NicolasCoubronne/Oulu_Embedded_Systems_Project/debug_code/motoring/Core/Inc/esp_arm.h

/*
 * esp_arm.h
 *
 *  Created on: Apr 26, 2023
 *      Author: tim
 *
 *      High-level functions for arm control (header)
 *      More documentation in implementation file
 */

#ifndef INC_ESP_ARM_H_
#define INC_ESP_ARM_H_

#include "stm32f4xx_hal.h"

int arm_angles_from_dist(unsigned int distance,
		unsigned int *angle_base_joint, unsigned int *angle_middle_joint, unsigned int *angle_claw_joint);
unsigned int offset_base_angle(unsigned int distance, double claw_offset);

#endif /* INC_ESP_ARM_H_ */
