NicolasCoubronne/Oulu_Embedded_Systems_Project/debug_code/motoring/Core/Src/esp_fsm.c

/*
 * esp_fsm.c
 *
 *  Created on: Apr 25, 2023
 *      Author: Jussi Virtanen
 *
 *  Robot arm state machine
 */

#include <stdio.h>
#include <math.h>
#include <stdlib.h>

#include "main.h"
#include "stm32f4xx_hal.h"
#include "tof.h"

#include "esp_ax12a.h"
#include "esp_arm.h"
#include "esp_fsm.h"
#include "esp_onboard.h"

extern UART_HandleTypeDef huart1;

//Bluetooth variables
extern uint8_t buf_RX[Size];
extern uint8_t buf_TX[Size];
uint8_t buf_len;

//TOF Variables
uint32_t refSpadCount;
uint8_t isApertureSpads;
uint8_t VhvSettings;
uint8_t PhaseCal;
VL53L0X_RangingMeasurementData_t RangingData;
static VL53L0X_Error myStatus = VL53L0X_ERROR_NONE;
unsigned int sensor_distance_mm;

/*
 * Send string to bluetooth
 *
 * msg: pointer to the message
 */
void bt_send(char *msg)
{
	HAL_UART_Transmit(&huart1, (uint8_t*)msg, strlen(msg), HAL_MAX_DELAY);
}

/*
 * Get distance value from TOF sensor
 *
 * returns: approximate distance in mm
 */
unsigned int get_dist() {
	unsigned int sensor_distance_mm= 0;

	for (int i=0; i<5; i++){
		myStatus = VL53L0X_PerformSingleRangingMeasurement(TOF1, &RangingData);
		if (myStatus!=VL53L0X_ERROR_NONE) {
			Error_Handler();
		}
		//if (RangingData.RangeMilliMeter < sensor_distance_mm) sensor_distance_mm = RangingData.RangeMilliMeter;
		sensor_distance_mm += RangingData.RangeMilliMeter;
		HAL_Delay(25);
	}

	sensor_distance_mm = sensor_distance_mm/5;

	/*
	myStatus = VL53L0X_PerformSingleRangingMeasurement(TOF1, &RangingData);
	if (myStatus!=VL53L0X_ERROR_NONE) {
		Error_Handler();
	}
	*/

	//while(RangingData.RangeStatus != 0) {}

	//sensor_distance_mm = RangingData.RangeMilliMeter;
	buf_len = sprintf((char*)buf_RX, "TOF value : %d\r\n", sensor_distance_mm);
	//bt_send((char*)buf_RX);


	if(sensor_distance_mm < 100) return 1000;

	return sensor_distance_mm;
}

/* Start the arm state machine
 * Further implementation details are in the documents
 */
void arm_start_sm()
{

	//Motors variables
	unsigned int angle_ccw_edge, angle_cw_edge; // Angles where object edge were found
	unsigned int middle_rot;
	unsigned int distance_threshold_mm; // max distance where arm will consider an object to exist
	unsigned int object_offset_distance_mm;
	unsigned int ccw_seek_angle_limit, cw_seek_angle_limit; // Seek area limits
	unsigned int claw_angle_limit_open, claw_angle_limit_closed;
	unsigned int dump_angle;
	unsigned int blocked_move_timeout_ms;
	unsigned int dist;
	unsigned int angle_middle_joint_max;
	double claw_offset_mm; // mm
	int status;
	armState arm_state;

	char temp[100];

	unsigned int angle_base_joint;
	unsigned int angle_middle_joint;
	unsigned int angle_claw_joint;

	// Heuristic offsets for distance and base rotation due to claw dimensions
	object_offset_distance_mm = -85;
	claw_offset_mm = 25.0;

	// From how far do we want to find the object
	distance_threshold_mm = 350;

	// Init limits and start values
	angle_middle_joint_max = 1000; // MAx angle for middle joint, if we go higher than this, then assume object too close
	ccw_seek_angle_limit = 205; // ~90 degrees ccw
	cw_seek_angle_limit = 819; // ~90 degrees cw
	claw_angle_limit_closed = 600; // fully closed
	claw_angle_limit_open = 320; // fully open
	dump_angle = 150; // Near max limit ccw
	angle_ccw_edge = angle_cw_edge = 0; // Use 0 as the magic number where angle has not yet been found
	blocked_move_timeout_ms = 2000;

	//TOF Init
	myStatus=TOF1_VL53L0X_Init_Single(&refSpadCount,&isApertureSpads,&VhvSettings,&PhaseCal,0);
	if (myStatus!=VL53L0X_ERROR_NONE) {
		printf("TOF1 Initialization Error : %i\r\n", myStatus);
	}
	TOFX_VL53L0X_LongRangeSettings(TOF1);
	VL53L0X_StartMeasurement (TOF1);

	// Test tof

	/*
	while (1) {
		sprintf(temp, "distance: %u\n", get_dist());
		bt_send(temp);
		HAL_Delay(100);
	}*/

	//MOTOR INIT
	uint8_t ids[] = {3, 2, 9, 8, 4};
	uint16_t init_angles[] = {390, 950, 600, claw_angle_limit_open, 819};
	uint16_t init_speed[] = {30, 60, 60, 40, 20};

	for (int i=0; i < sizeof(ids)/sizeof(ids[0]); i++) {
		ax_set_move_speed(ids[i], init_speed[i]);
		HAL_Delay(500);
	}
	ax_set_max_torque(8, 200);


	arm_state = ARM_MOVE_TO_IDLE;
	while(1) {
		switch(arm_state) {

		case ARM_MOVE_TO_IDLE:
			bt_send("Entering state : ARM_MOVE_TO_IDLE\r\n");
			sprintf(temp, "Voltage data from sensor: %f\r\n", get_current_measure());
			bt_send(temp);
			// Reset object edges
			angle_ccw_edge = angle_cw_edge = 0;
			//Move to good idle position (blocked move)
			for (int i=0; i < sizeof(ids)/sizeof(ids[0]); i++) {
				ax_move_blocked(ids[i], init_angles[i], blocked_move_timeout_ms);
			}
			arm_state = ARM_SEEK_CCW;

			break;

		case ARM_SEEK_CCW:
			bt_send("Entering state : ARM_SEEK_CCW\r\n");
			set_operation_led(LED_BLINK);
			angle_ccw_edge = angle_cw_edge = 0;
			// Set goal to ccw edge if not yet set
			ax_stop(4);
			HAL_Delay(500);
			ax_set_goal_raw(4, ccw_seek_angle_limit);
			while(1){
				// If at edge, invert seek direction
				if (ax_diff_from_goal(4) <= 10) {
					HAL_Delay(1000);
					arm_state = ARM_SEEK_CW;
					break;
				}
				// cw edge found
				if ((dist = get_dist()) < distance_threshold_mm) {
					angle_cw_edge = ax_get_current_position(4);
					sprintf(temp, "Object edge CW angle: %u\r\n", angle_cw_edge);
					bt_send(temp);
					arm_state = ARM_SEEK_EDGE_CCW;
					break;
				}
				HAL_Delay(50);
			}

			break;

		case ARM_SEEK_EDGE_CCW:
			bt_send("Entering state : ARM_SEEK_EDGE_CCW\r\n");
			// Set goal to ccw edge if not yet set
			ax_stop(4);
			HAL_Delay(500);
			ax_set_goal_raw(4, ccw_seek_angle_limit);
			while(1){
				// If at edge, go to beginning (error)
				if (ax_diff_from_goal(4) <= 10) {
					HAL_Delay(1000);
					arm_state = ARM_MOVE_TO_IDLE;
					break;
				}
				// ccw edge found with cw edge found
				if ((dist = get_dist()) > distance_threshold_mm) {
					angle_ccw_edge = ax_get_current_position(4);
					sprintf(temp, "Object edge CCW angle: %u\r\n", angle_ccw_edge);
					bt_send(temp);
					ax_stop(4);
					arm_state = ARM_MOVE_TO_GRAB;

					break;
				}
				HAL_Delay(50);
			}

			break;

		case ARM_SEEK_CW:
			bt_send("Entering state : ARM_SEEK_CW\r\n");
			angle_ccw_edge = angle_cw_edge = 0;
			// Set goal to cw edge if not yet set
			ax_stop(4);
			HAL_Delay(500);
			ax_set_goal_raw(4, cw_seek_angle_limit);
			while(1){
				// If at edge, invert seek direction
				if (ax_diff_from_goal(4) <= 10) {
					HAL_Delay(1000);
					arm_state = ARM_SEEK_CCW;
					break;
				}
				// ccw edge found
				if ((dist = get_dist()) < distance_threshold_mm) {
					angle_ccw_edge = ax_get_current_position(4);
					sprintf(temp, "Object edge CCW angle: %u\r\n", angle_ccw_edge);
					bt_send(temp);
					arm_state = ARM_SEEK_EDGE_CW;
					break;
				}

				HAL_Delay(50);
			}

			break;

		case ARM_SEEK_EDGE_CW:
			bt_send("Entering state : ARM_SEEK_EDGE_CW\r\n");
			// Set goal to cw edge if not yet set
			ax_stop(4);
			HAL_Delay(500);
			ax_set_goal_raw(4, cw_seek_angle_limit);
			while(1){
				// If at edge, go to beginning (error)
				if (ax_diff_from_goal(4) <= 10) {
					HAL_Delay(1000);
					arm_state = ARM_MOVE_TO_IDLE;
					break;
				}
				// ccw edge found with cw edge found
				if (get_dist() > distance_threshold_mm) {
					angle_cw_edge = ax_get_current_position(4);
					sprintf(temp, "Object edge CW angle: %u\r\n", angle_cw_edge);
					bt_send(temp);
					ax_stop(4);
					arm_state = ARM_MOVE_TO_GRAB;

					break;
				}
				HAL_Delay(50);
			}

			break;

		case ARM_MOVE_TO_GRAB:
			bt_send("Entering state : ARM_MOVE_TO_GRAB\r\n");
			set_operation_led(LED_ON);
			ax_stop(4);
			HAL_Delay(500);
			middle_rot = (angle_ccw_edge + angle_cw_edge) / 2;
			sprintf(temp, "Object middle point angle: %u\r\n", middle_rot);
			bt_send(temp);
			ax_move_blocked(4, middle_rot, blocked_move_timeout_ms);
			//find rotation angles for correct distance, move inblocked mode
			unsigned int distance = get_dist();

			while(distance > distance_threshold_mm) distance = get_dist();
			sprintf(temp, "Object middle point distance: %u\r\n", distance);
			bt_send(temp);
			status = arm_angles_from_dist(distance+object_offset_distance_mm, &angle_base_joint,  &angle_middle_joint, &angle_claw_joint);
			if (status == -1) {
				bt_send("ERROR: Object is too close. Move object to proper distance. Resetting operation.\r\n");
				arm_state = ARM_ERROR_STATE;
			} else if (status == 1) {
				bt_send("ERROR: Object is too far. Consider adjusting max seeking threshold. Resetting operation.\r\n");
				arm_state = ARM_ERROR_STATE;
			} else if (angle_middle_joint > angle_middle_joint_max) {
				bt_send("ERROR: Impossible angle for middle joint, object is too close. Move object to proper distance. Resetting operation.\r\n");
				arm_state = ARM_ERROR_STATE;
			} else {
				ax_move_blocked(4, middle_rot - offset_base_angle(distance+object_offset_distance_mm, claw_offset_mm), blocked_move_timeout_ms);
				ax_move_blocked(9, angle_claw_joint, blocked_move_timeout_ms);
				ax_move_blocked(2, angle_middle_joint, blocked_move_timeout_ms);
				ax_move_blocked(3, angle_base_joint, blocked_move_timeout_ms);
				ax_move_blocked(2, angle_middle_joint - 20, blocked_move_timeout_ms);
				ax_move_blocked(9, angle_claw_joint - 10, blocked_move_timeout_ms);
				ax_move_blocked(2, angle_middle_joint - 40, blocked_move_timeout_ms);
				HAL_Delay(2000); // Super janky movement so wait even more
				arm_state = ARM_GRAB_CLAW;
			}

			break;

		case ARM_GRAB_CLAW:
			bt_send("Entering state : ARM_GRAB_CLAW\r\n");
			sprintf(temp, "Voltage data from sensor: %f\r\n", get_current_measure());
			bt_send(temp);
			ax_move_blocked(8, claw_angle_limit_closed, blocked_move_timeout_ms);
			if (ax_diff_from_goal(8) < 15) {
				bt_send("ERROR: failed to grab object.\r\n");
				arm_state = ARM_ERROR_STATE;
			} else {
				arm_state = ARM_MOVE_TO_DUMP;
			}

			break;

		case ARM_MOVE_TO_DUMP:
			bt_send("Entering state : ARM_MOVE_TO_DUMP\r\n");
			ax_move_blocked(3, 512, blocked_move_timeout_ms);
			ax_move_blocked(2, 819, blocked_move_timeout_ms);
			ax_move_blocked(9, 512, blocked_move_timeout_ms);
			ax_move_blocked(4, dump_angle, blocked_move_timeout_ms);
			ax_move_blocked(2, 810, blocked_move_timeout_ms);
			ax_move_blocked(9, 730, blocked_move_timeout_ms);
			ax_move_blocked(3, 700, blocked_move_timeout_ms);
			ax_move_blocked(8, claw_angle_limit_open, blocked_move_timeout_ms);
			ax_move_blocked(2, 880, blocked_move_timeout_ms);
			ax_move_blocked(4, dump_angle-10, blocked_move_timeout_ms);
			arm_state = ARM_MOVE_TO_IDLE;

			break;

		case ARM_ERROR_STATE:
			bt_send("Entering state : ARM_ERROR_STATE\r\n");
			//while(1){}
			set_error_led(LED_ON);
			HAL_Delay(5000);
			set_error_led(LED_OFF);
			arm_state = ARM_MOVE_TO_IDLE;

			break;

		default:
			break;
		}
	}
}
