NicolasCoubronne/Oulu_Embedded_Systems_Project/debug_code/motoring/Core/Inc/demos.h

/*
 * demos.h
 *
 *  Created on: Apr 21, 2023
 *      Author: tim
 *
 *      Demo codes for the arm operations (header)
 *      More documentation in implementation file
 */

#ifndef INC_DEMOS_H_
#define INC_DEMOS_H_

void demo1();
void demo2();
void demo_load();
void print_angles();

#endif /* INC_DEMOS_H_ */
